Alcyone-0022/SandPomo/Flow_Chart/2.2_flow_chart.png

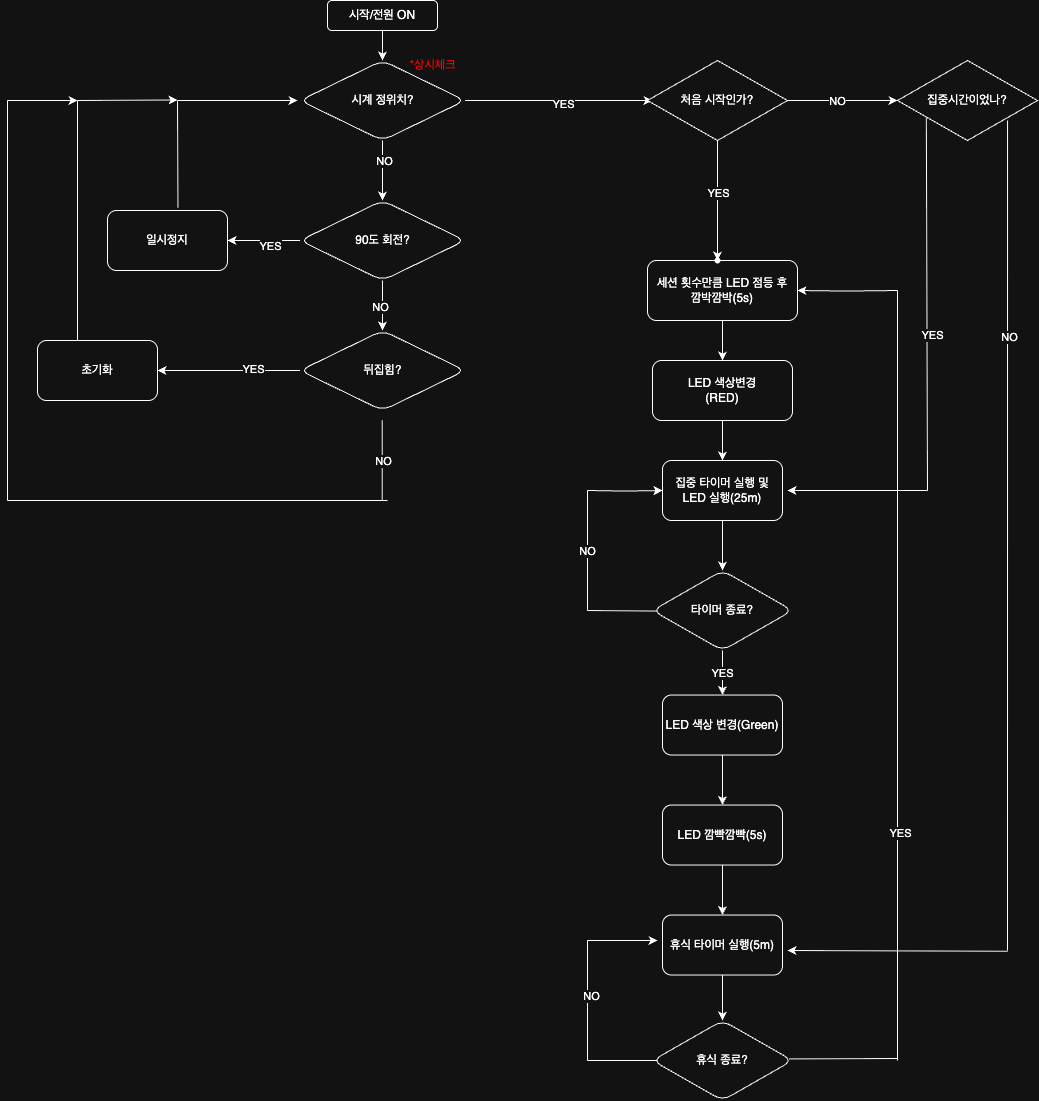
Flow_Chart/2.2_flow_chart.png
